Adizero17/Ant-Bot1/CAD-Daten/Chassi/Chassi_7 (Leichtbau geschlossen).SLDPRT

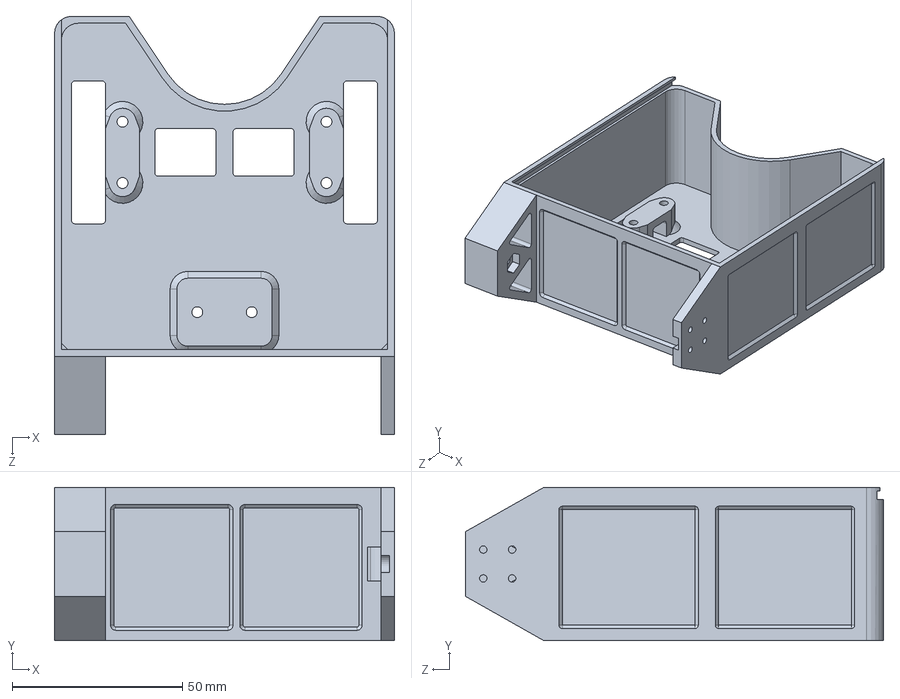
[picture p48: CAD file, 2019-05-29]
CAD-Daten/Chassi/Chassi_7 (Leichtbau geschlossen).SLDPRT
100.0 x 45.0 x 123.0 mm
