Adizero17/Ant-Bot1/CAD-Daten/Deckel/Deckel_3.SLDPRT

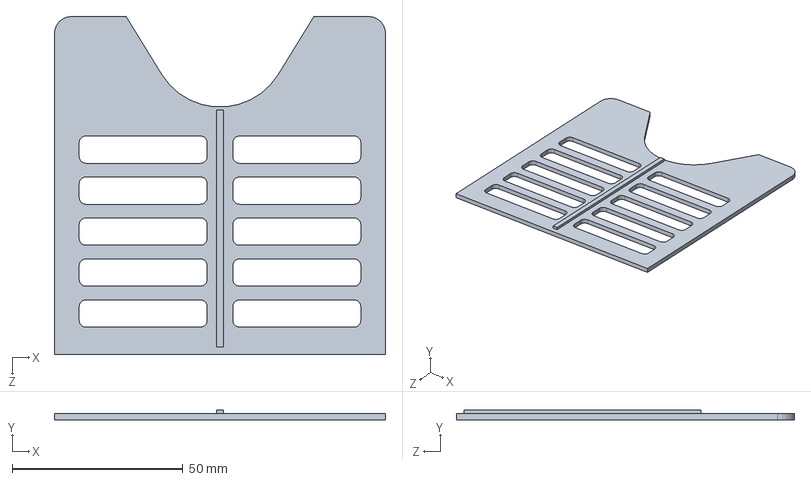
[picture p49: CAD file, 2019-05-29]
CAD-Daten/Deckel/Deckel_3.SLDPRT
97.0 x 2.80 x 99.0 mm
