Adizero17/Ant-Bot1/CAD-Daten/Final Version/V-Tec_MicroMotor_6V.SLDPRT

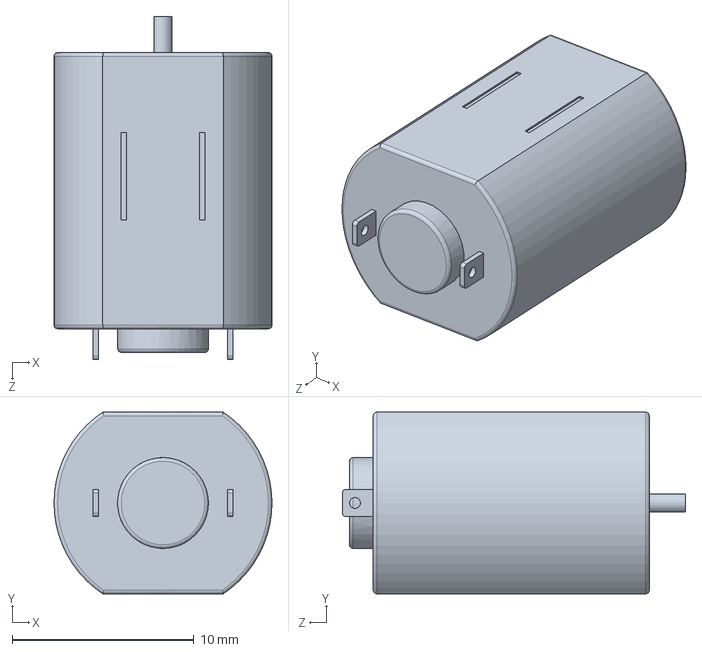
[picture p50: CAD file, 2019-06-19]
CAD-Daten/Final Version/V-Tec_MicroMotor_6V.SLDPRT
12.0 x 10.0 x 18.9 mm
