Adizero17/Ant-Bot1/CAD-Daten/Waffenelement/Hülse_4.STL

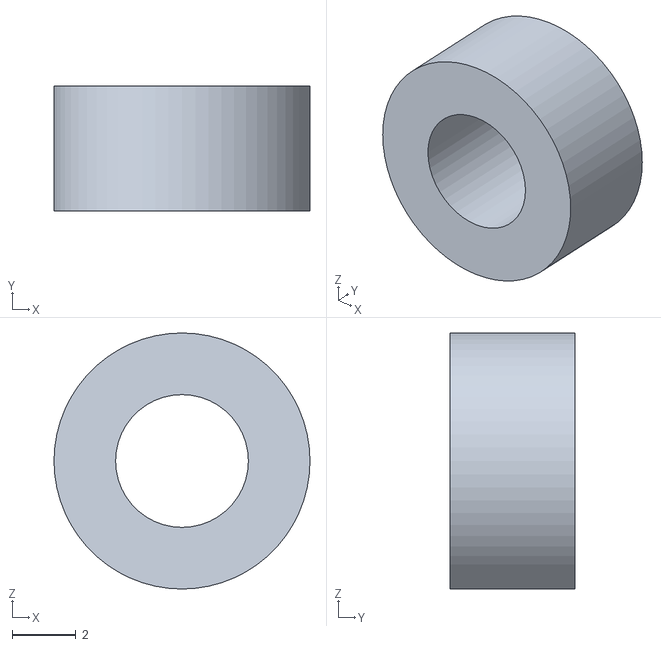
[picture p51: CAD file, 2019-06-04]
CAD-Daten/Waffenelement/Hülse_4.STL
8.00 x 3.90 x 8.00
