Adizero17/Ant-Bot1/CAD-Daten/Chassi/Chassi_5 (Schraubenänderung).SLDPRT

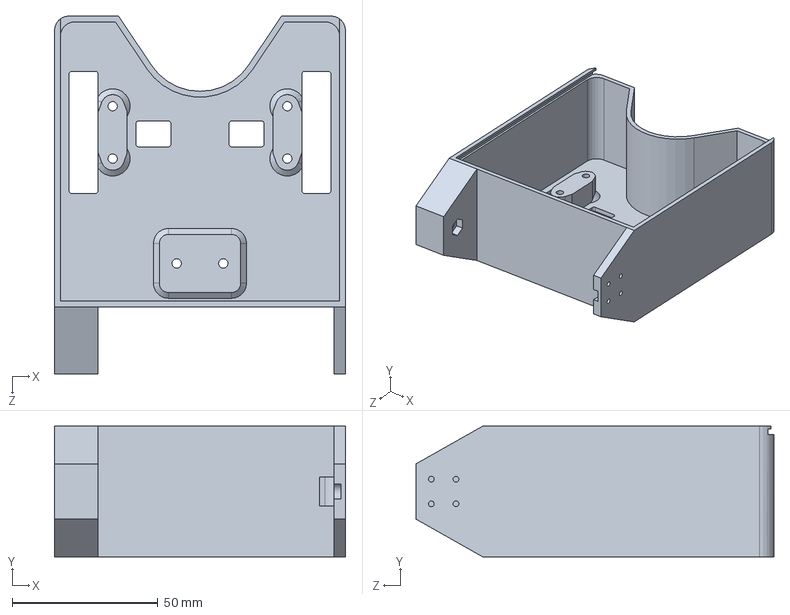
[picture p52: CAD file, 2019-05-23]
CAD-Daten/Chassi/Chassi_5 (Schraubenänderung).SLDPRT
100.0 x 45.0 x 123.0 mm
