Adizero17/Ant-Bot1/CAD-Daten/Deckel/Deckel_2.SLDPRT

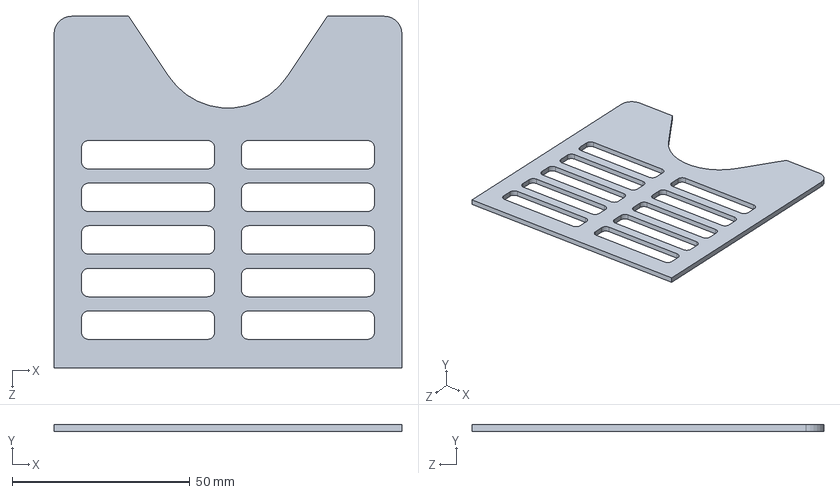
[picture p53: CAD file, 2019-05-21]
CAD-Daten/Deckel/Deckel_2.SLDPRT
98.0 x 2.00 x 99.0 mm
