Adizero17/Ant-Bot1/CAD-Daten/Final Version/Chassi_Final.SLDPRT

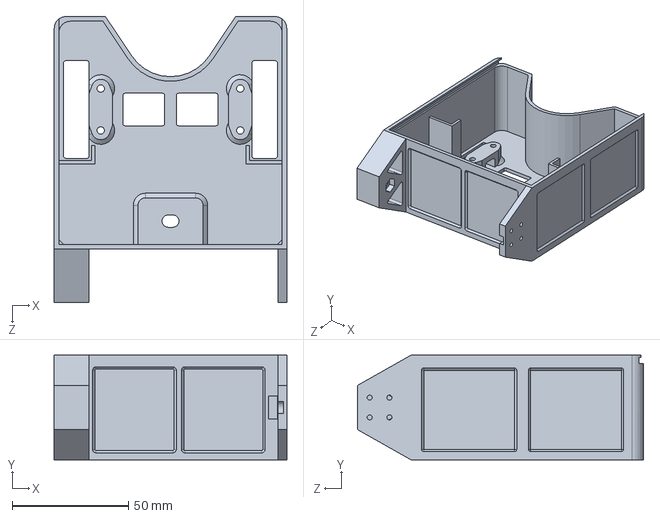
[picture p54: CAD file, 2019-06-19]
CAD-Daten/Final Version/Chassi_Final.SLDPRT
100.0 x 45.0 x 123.0 mm
