Adizero17/Ant-Bot1/CAD-Daten/Waffenelement/Hülse_3.SLDPRT

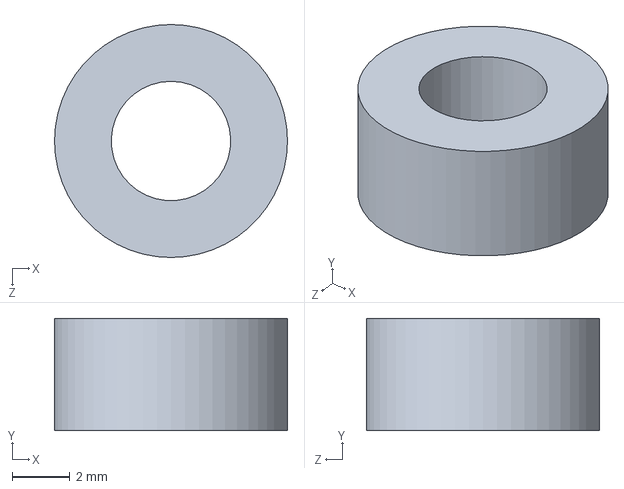
[picture p55: CAD file, 2019-06-04]
CAD-Daten/Waffenelement/Hülse_3.SLDPRT
8.10 x 3.90 x 8.10 mm
