Adizero17/Ant-Bot1/CAD-Daten/Deckel/Deckel_1.SLDPRT

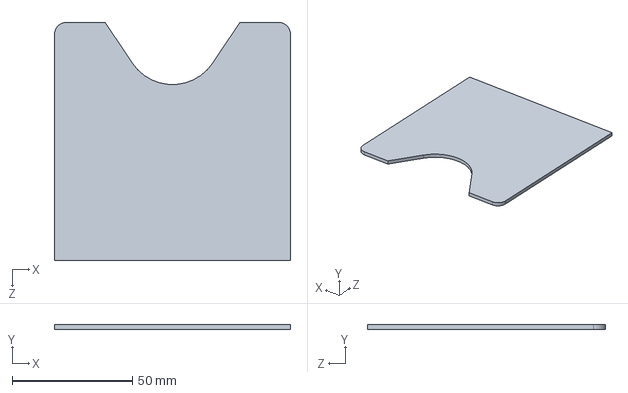
[picture p56: CAD file, 2019-05-20]
CAD-Daten/Deckel/Deckel_1.SLDPRT
98.0 x 2.00 x 99.0 mm
