Adizero17/Ant-Bot1/CAD-Daten/Waffenelement/Hülse_2.SLDPRT

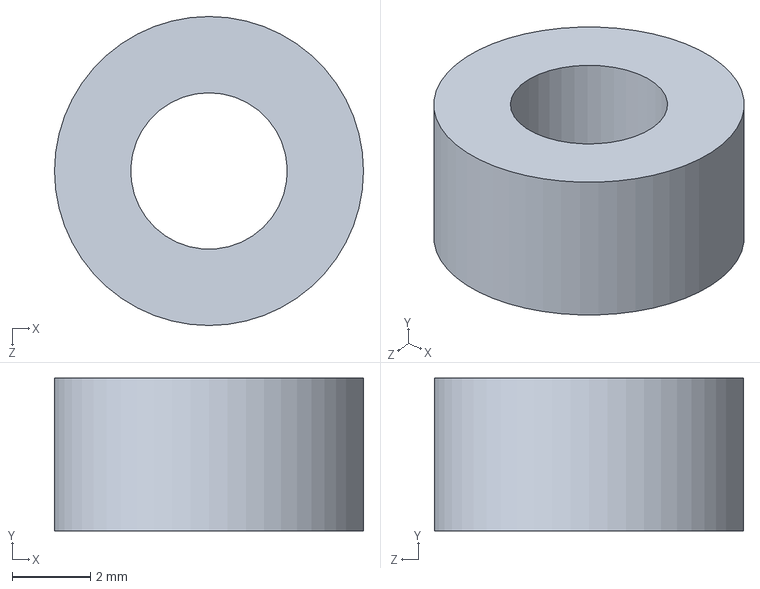
[picture p57: CAD file, 2019-06-04]
CAD-Daten/Waffenelement/Hülse_2.SLDPRT
7.90 x 3.90 x 7.90 mm
