Adizero17/Ant-Bot1/CAD-Daten/Chassi/Chassi_1.SLDPRT

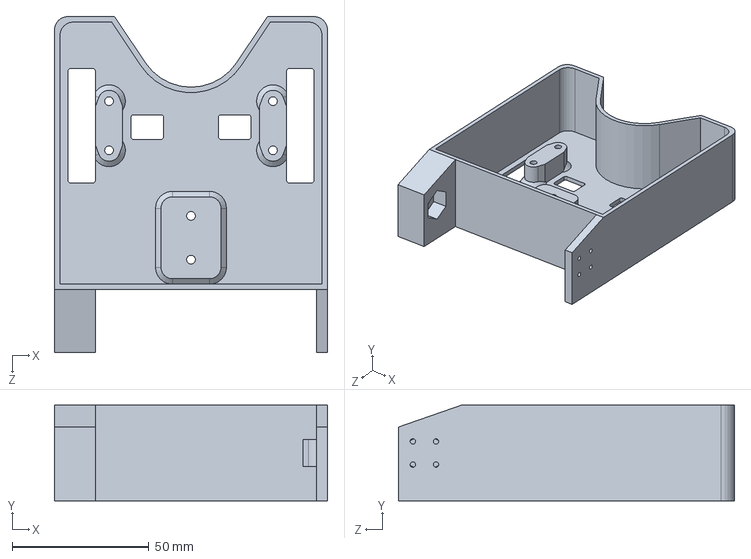
[picture p58: CAD file, 2019-05-21]
CAD-Daten/Chassi/Chassi_1.SLDPRT
100.0 x 35.0 x 123.0 mm
