Adizero17/Ant-Bot1/CAD-Daten/Chassi/Chassi_2.SLDPRT

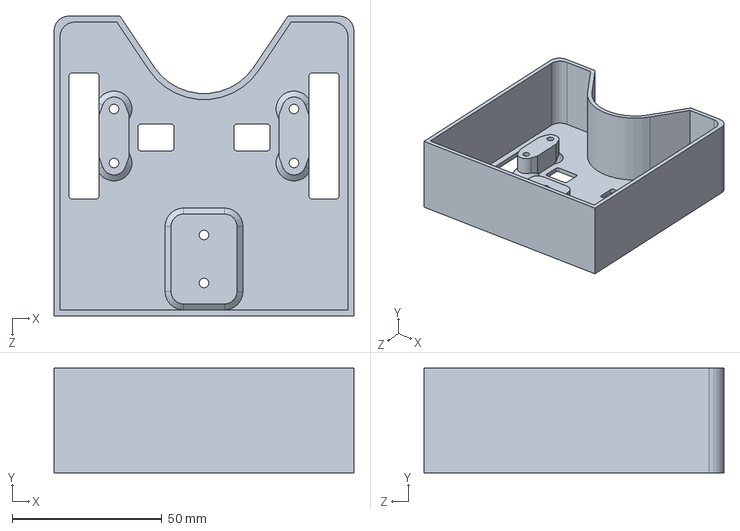
[picture p59: CAD file, 2019-05-21]
CAD-Daten/Chassi/Chassi_2.SLDPRT
100.0 x 35.0 x 100.0 mm
