Adizero17/Ant-Bot1/CAD-Daten/Waffenelement/Hülse.SLDPRT

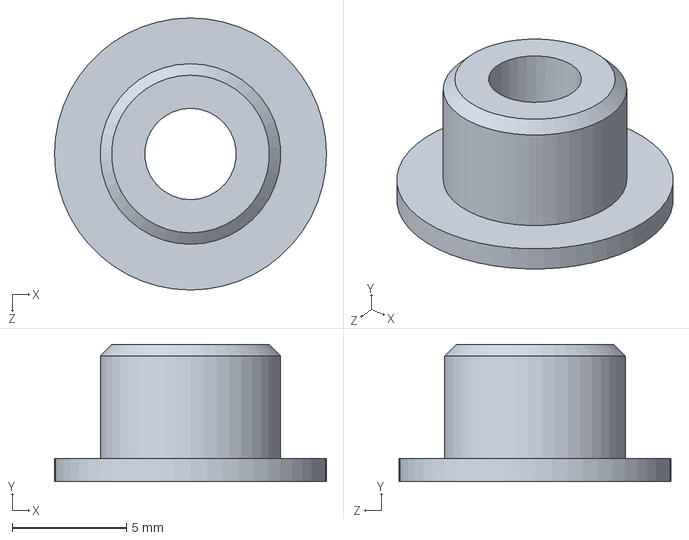
[picture p60: CAD file, 2019-06-03]
CAD-Daten/Waffenelement/Hülse.SLDPRT
11.9 x 6.00 x 11.9 mm
