Adizero17/Ant-Bot1/CAD-Daten/Waffenelement/Walze_4 mit Nupsis.SLDPRT

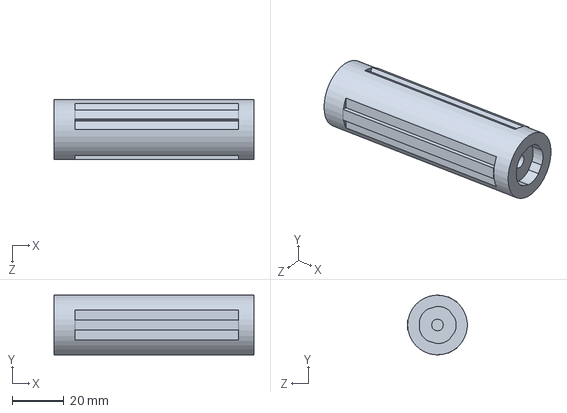
[picture p61: CAD file, 2019-06-03]
CAD-Daten/Waffenelement/Walze_4 mit Nupsis.SLDPRT
77.0 x 23.0 x 23.0 mm
