Adizero17/Ant-Bot1/CAD-Daten/Final Version/Walze_Final.SLDPRT

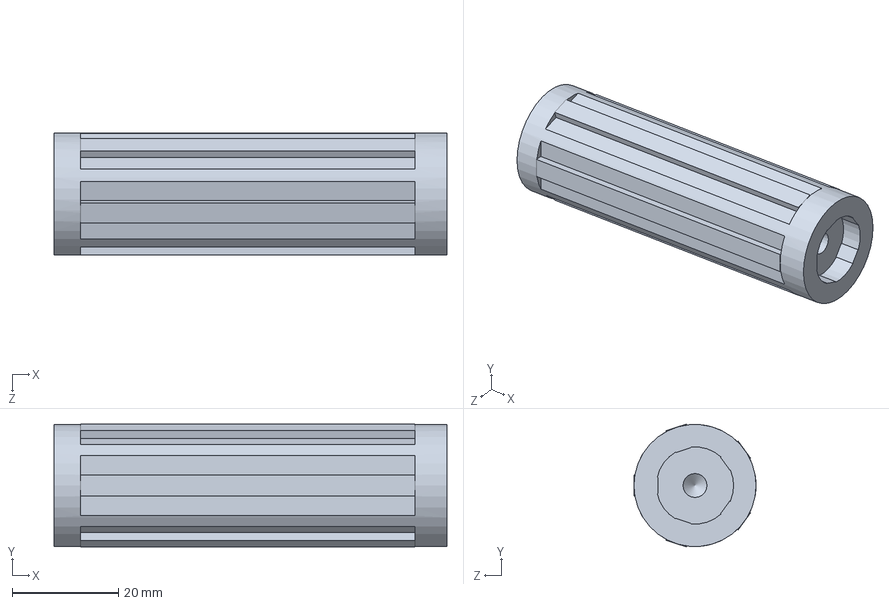
[picture p62: CAD file, 2019-06-19]
CAD-Daten/Final Version/Walze_Final.SLDPRT
74.0 x 23.1 x 23.0 mm
