Adizero17/Ant-Bot1/CAD-Daten/Waffenelement/Walze_2.SLDPRT

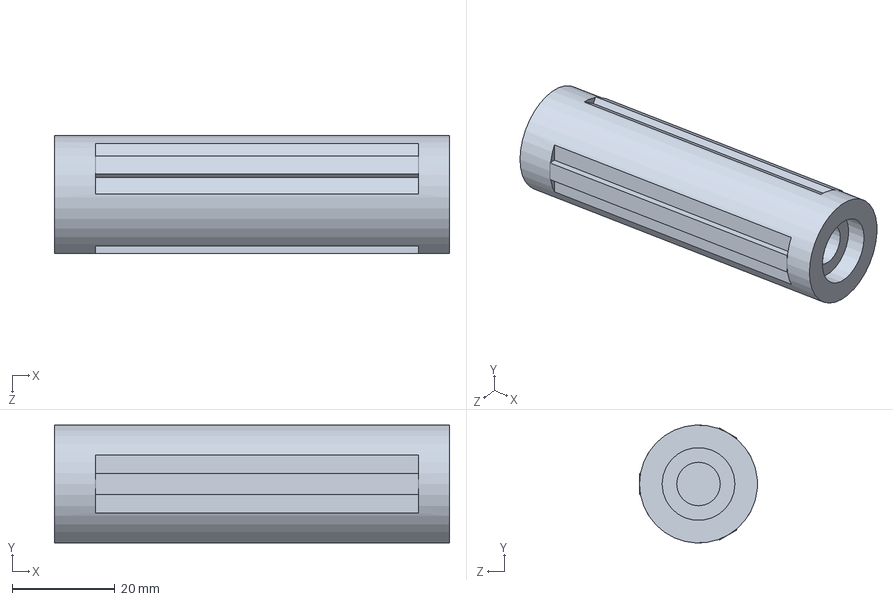
[picture p63: CAD file, 2019-05-21]
CAD-Daten/Waffenelement/Walze_2.SLDPRT
77.0 x 23.0 x 23.0 mm
