Adizero17/Ant-Bot1/CAD-Daten/Final Version/V-Tec_GetriebeHalter.SLDPRT

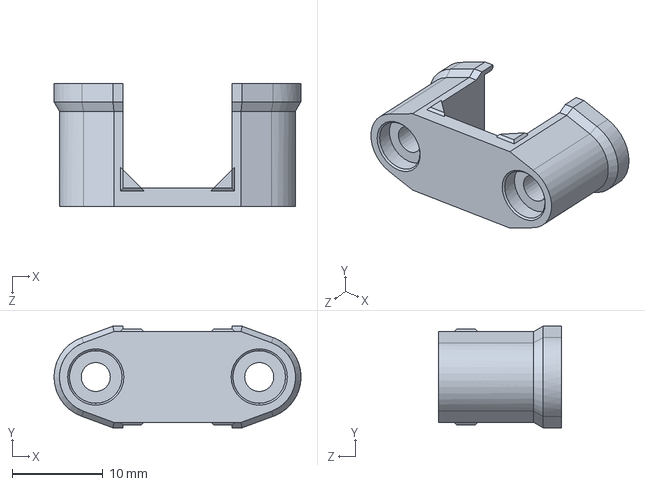
[picture p64: CAD file, 2019-06-19]
CAD-Daten/Final Version/V-Tec_GetriebeHalter.SLDPRT
27.2 x 11.2 x 13.5 mm
