Adizero17/Ant-Bot1/CAD-Daten/Final Version/Lipo_2S_350mA_LemonRC.SLDPRT

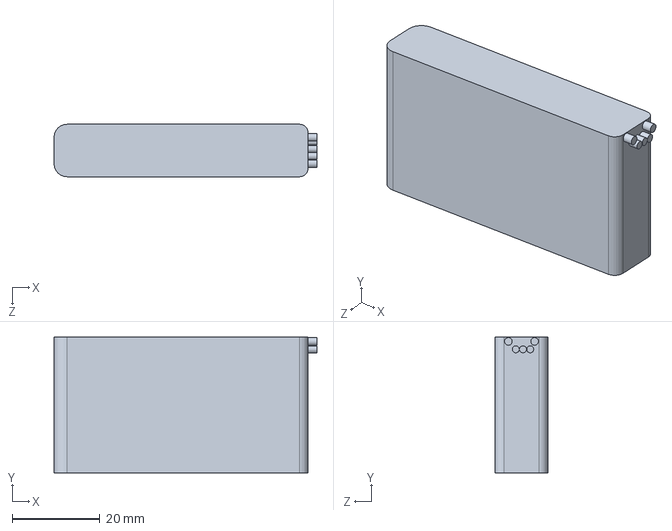
[picture p65: CAD file, 2019-05-21]
CAD-Daten/Final Version/Lipo_2S_350mA_LemonRC.SLDPRT
60.0 x 31.0 x 12.0 mm
