Adizero17/Ant-Bot1/CAD-Daten/Final Version/Kugellager.SLDPRT

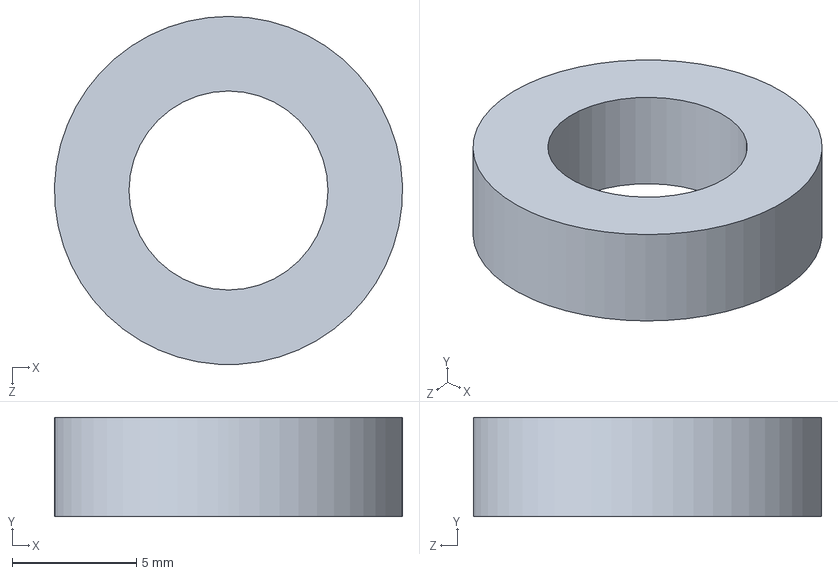
[picture p66: CAD file, 2019-05-20]
CAD-Daten/Final Version/Kugellager.SLDPRT
14.0 x 4.00 x 14.0 mm
