Adizero17/Ant-Bot1/CAD-Daten/Final Version/Motor.SLDPRT

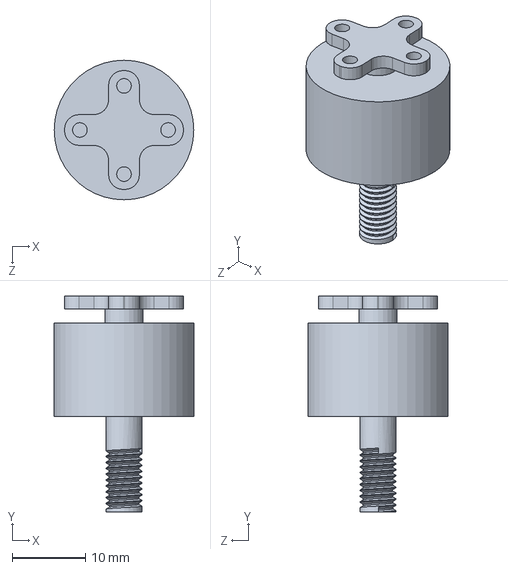
[picture p67: CAD file, 2019-05-20]
CAD-Daten/Final Version/Motor.SLDPRT
19.0 x 29.4 x 19.0 mm
