Adizero17/Ant-Bot1/CAD-Daten/Final Version/Pololu_Wheel_40x7_Felge.SLDPRT

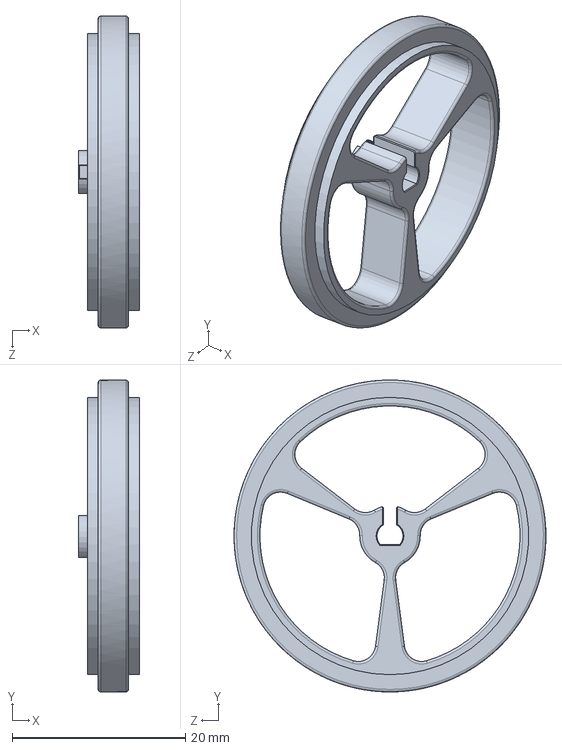
[picture p68: CAD file, 2019-04-09]
CAD-Daten/Final Version/Pololu_Wheel_40x7_Felge.SLDPRT
7.00 x 36.0 x 36.0 mm
