Adizero17/Ant-Bot1/CAD-Daten/Final Version/V-Tec_DistanzRohr.SLDPRT

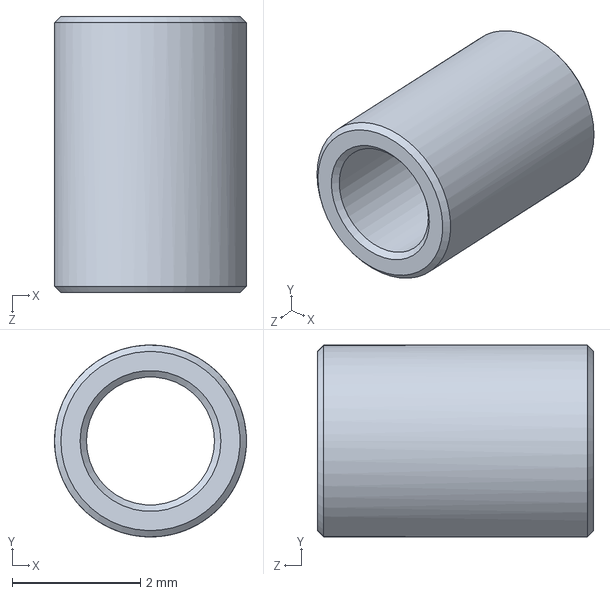
[picture p69: CAD file, 2019-04-09]
CAD-Daten/Final Version/V-Tec_DistanzRohr.SLDPRT
3.00 x 3.00 x 4.32 mm
