Adizero17/Ant-Bot1/CAD-Daten/Final Version/PololuWheel_40x7_Reifen.SLDPRT

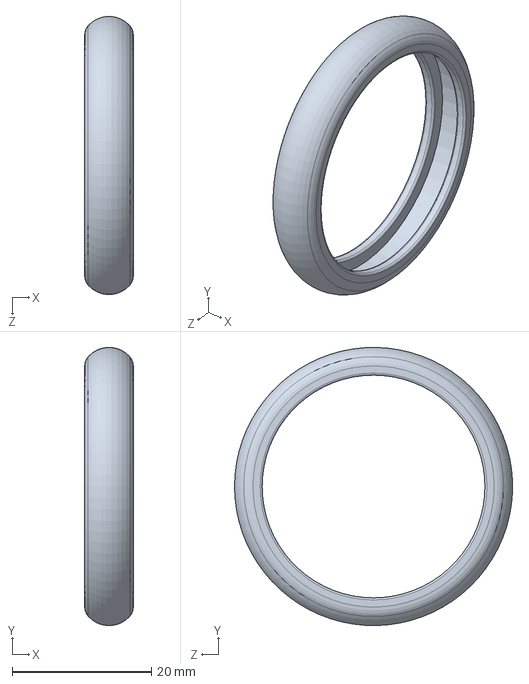
[picture p70: CAD file, 2019-04-09]
CAD-Daten/Final Version/PololuWheel_40x7_Reifen.SLDPRT
7.00 x 40.0 x 39.9 mm
