Adizero17/Ant-Bot1/CAD-Daten/Final Version/Kugel 12mm.SLDPRT

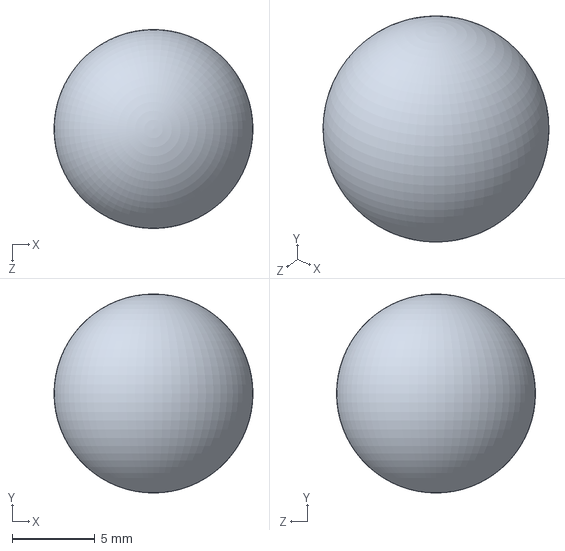
[picture p71: CAD file, 2019-04-09]
CAD-Daten/Final Version/Kugel 12mm.SLDPRT
12.0 x 12.0 x 12.0 mm
