Adizero17/Ant-Bot1/CAD-Daten/Final Version/V-Tec_GetriebePlatteMockup.SLDPRT

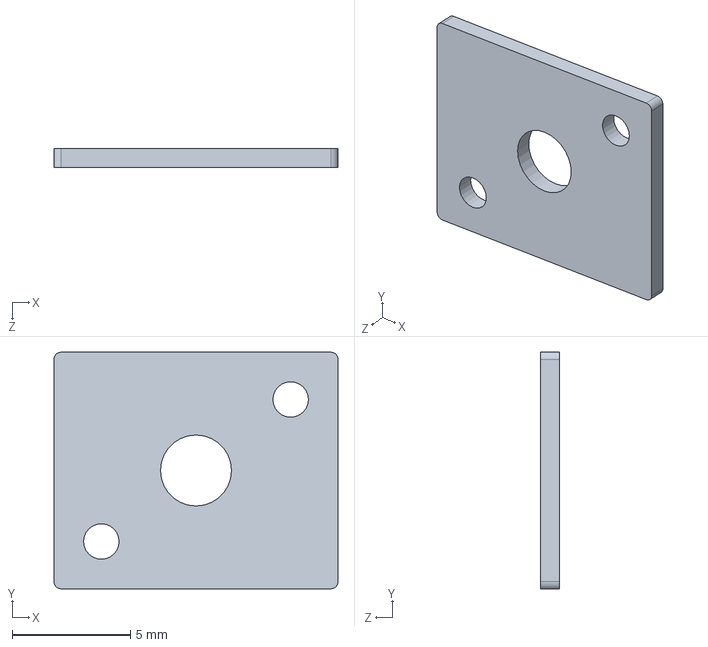
[picture p72: CAD file, 2019-04-09]
CAD-Daten/Final Version/V-Tec_GetriebePlatteMockup.SLDPRT
12.0 x 10.0 x 0.8 mm
