Adizero17/Ant-Bot1/CAD-Daten/Final Version/V-Tec_AntriebsWelle.SLDPRT

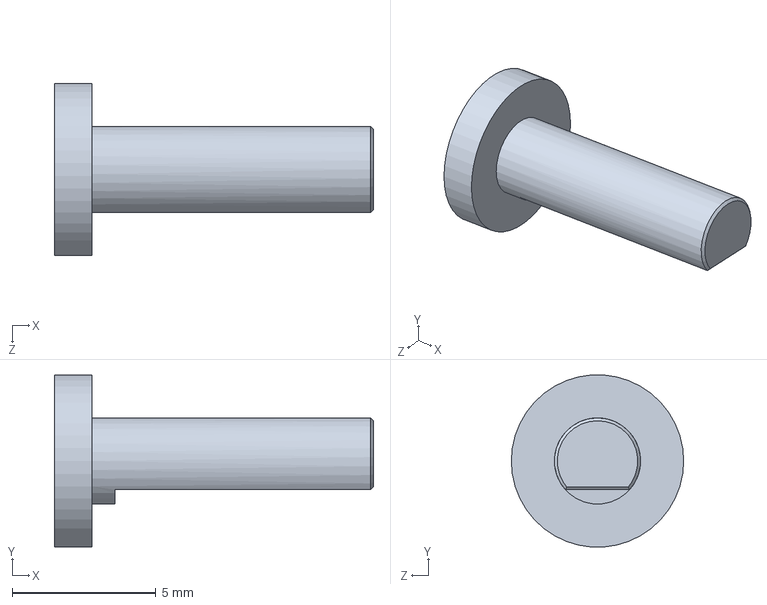
[picture p73: CAD file, 2019-04-09]
CAD-Daten/Final Version/V-Tec_AntriebsWelle.SLDPRT
11.1 x 5.98 x 6.00 mm
