Adizero17/Ant-Bot1/CAD-Daten/Final Version/KugelAufnahme.SLDPRT

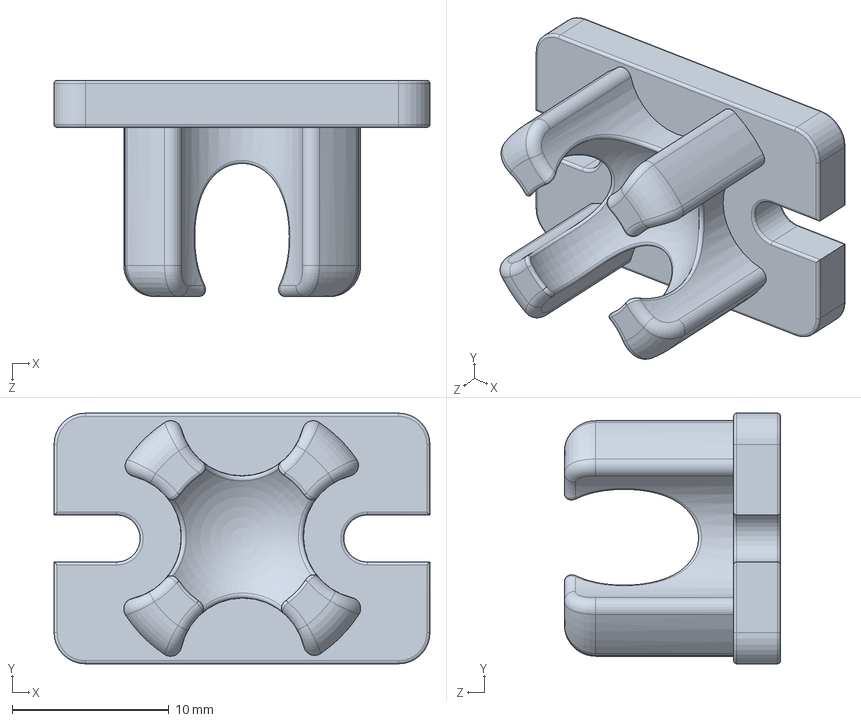
[picture p74: CAD file, 2019-04-09]
CAD-Daten/Final Version/KugelAufnahme.SLDPRT
24.0 x 16.0 x 13.8 mm
